timborn/SWR-Protector/docs/case end 1.jpg

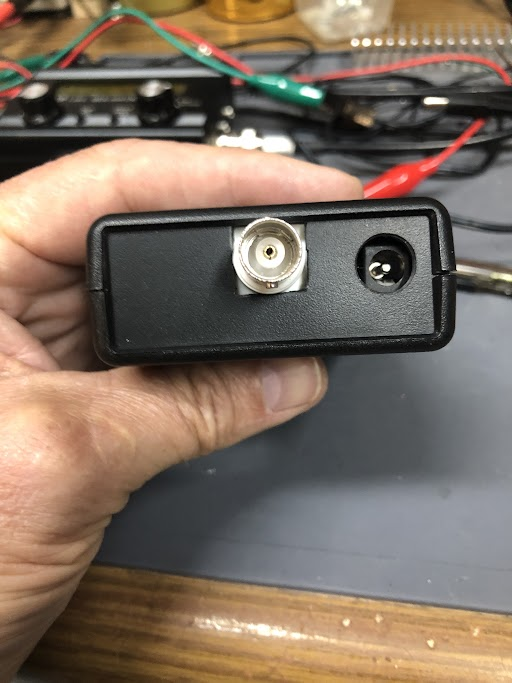
docs/case end 1.jpg
