timborn/SWR-Protector/docs/case end 2.jpg

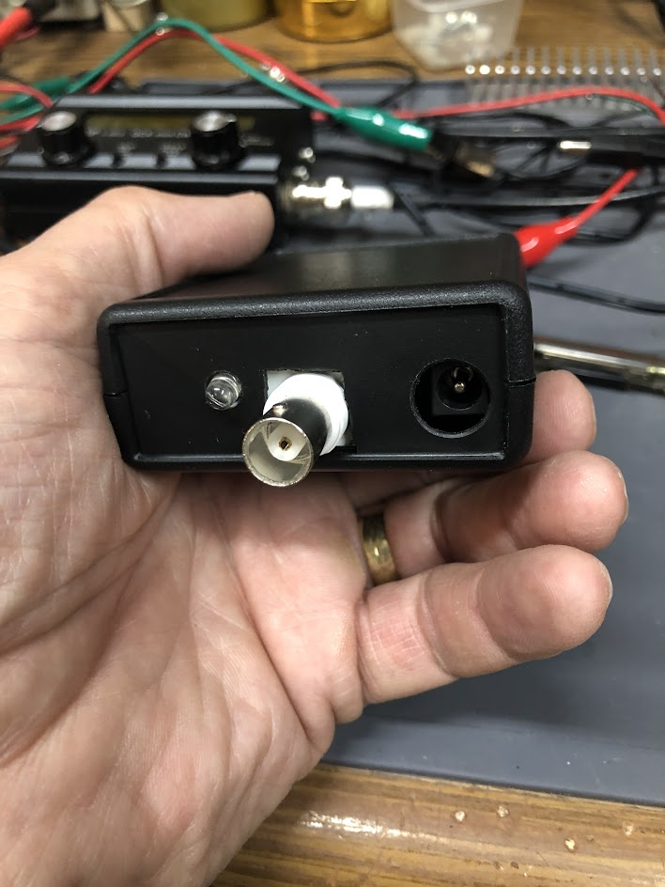
docs/case end 2.jpg
