timborn/SWR-Protector/docs/PCB v0.5.jpg

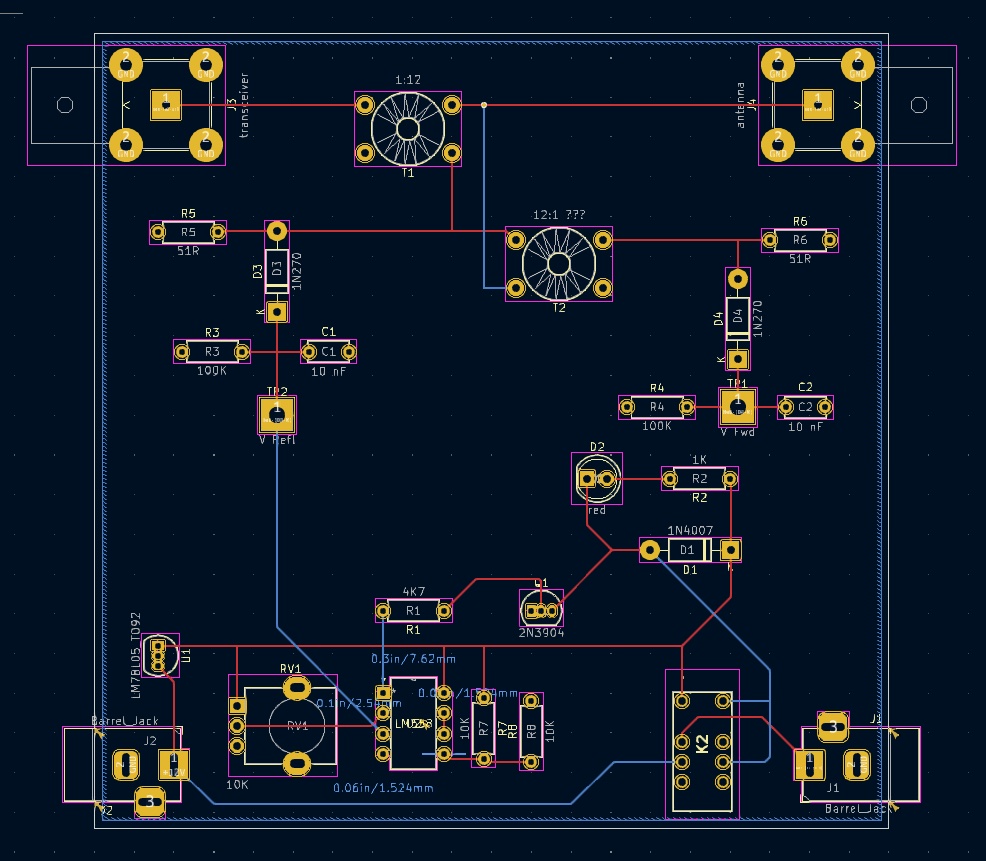
docs/PCB v0.5.jpg
