timborn/SWR-Protector/docs/v0.6 3D view.png

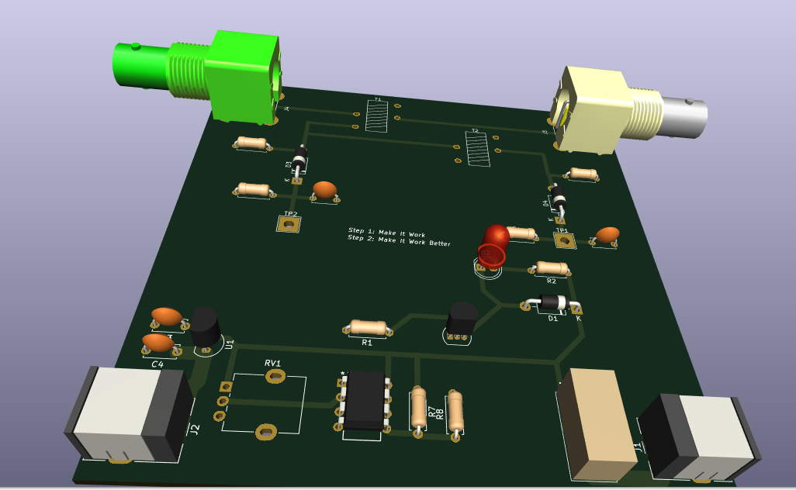
docs/v0.6 3D view.png
