timborn/SWR-Protector/docs/v1.0/SWR Protector Bottom.jpg

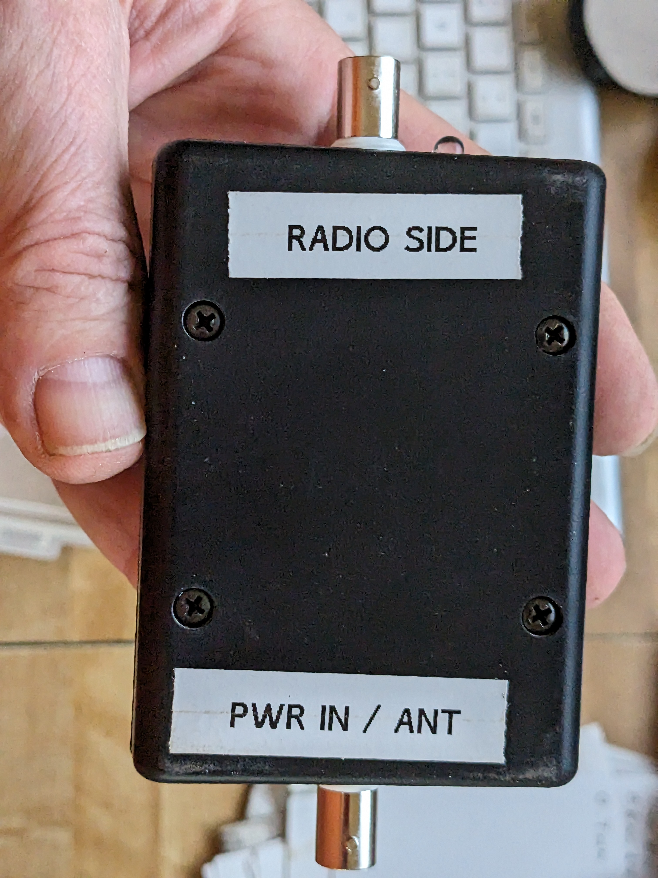
docs/v1.0/SWR Protector Bottom.jpg
