timborn/SWR-Protector/docs/v1.0/SWR Protector Radio Side.jpg

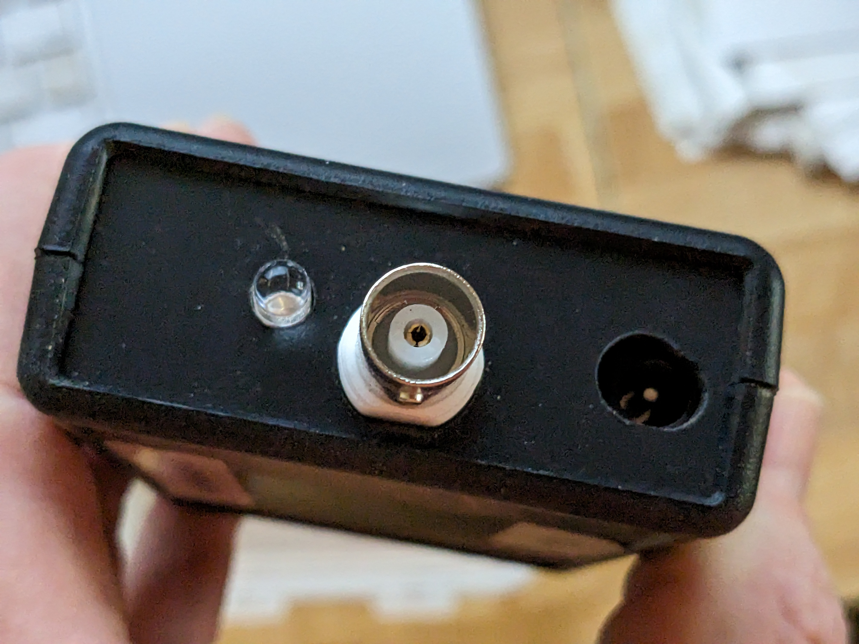
docs/v1.0/SWR Protector Radio Side.jpg
