timborn/SWR-Protector/docs/v1.0/SWR Protector V1.jpg

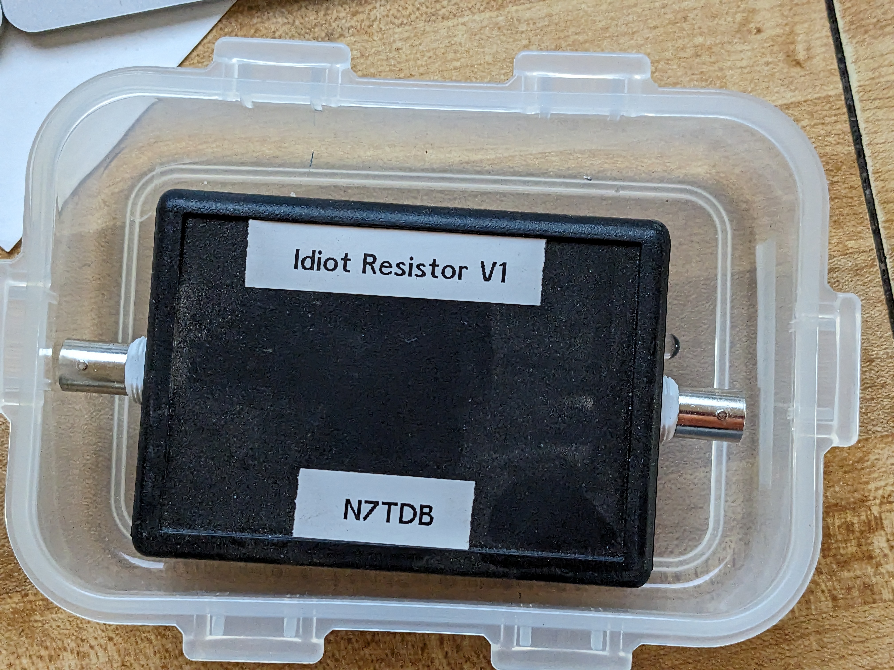
docs/v1.0/SWR Protector V1.jpg
