timborn/SWR-Protector/docs/v1.0/V1.0 It Works.jpg

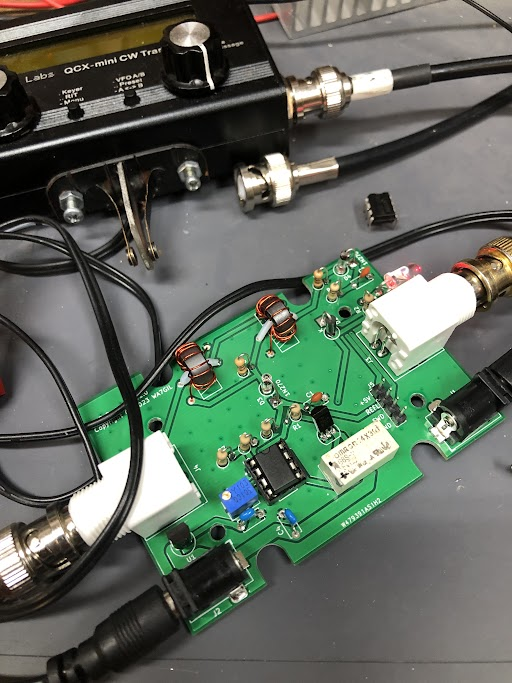
docs/v1.0/V1.0 It Works.jpg
