timborn/SWR-Protector/docs/v1.0/V1.0 shutdown 1.6ms.jpg

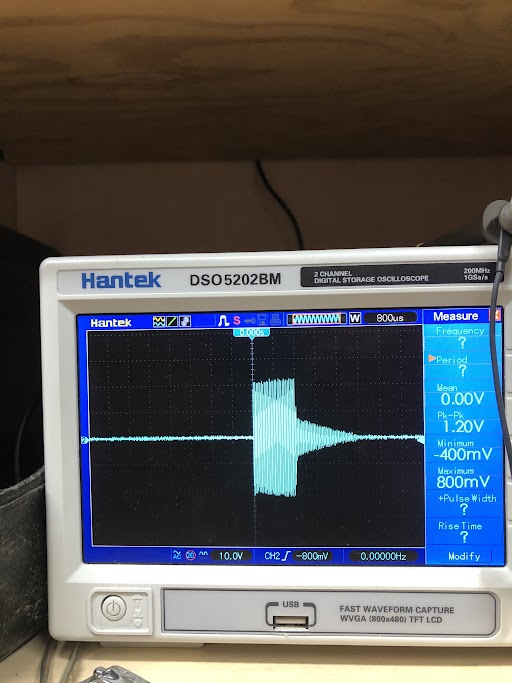
docs/v1.0/V1.0 shutdown 1.6ms.jpg
