timborn/SWR-Protector/docs/prototype.jpg

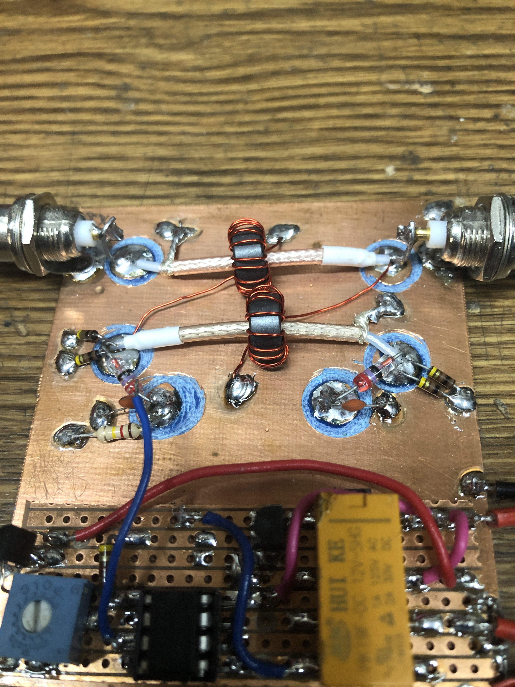
docs/prototype.jpg
